IvanNaum/pwm_generator/imgs/E3.png

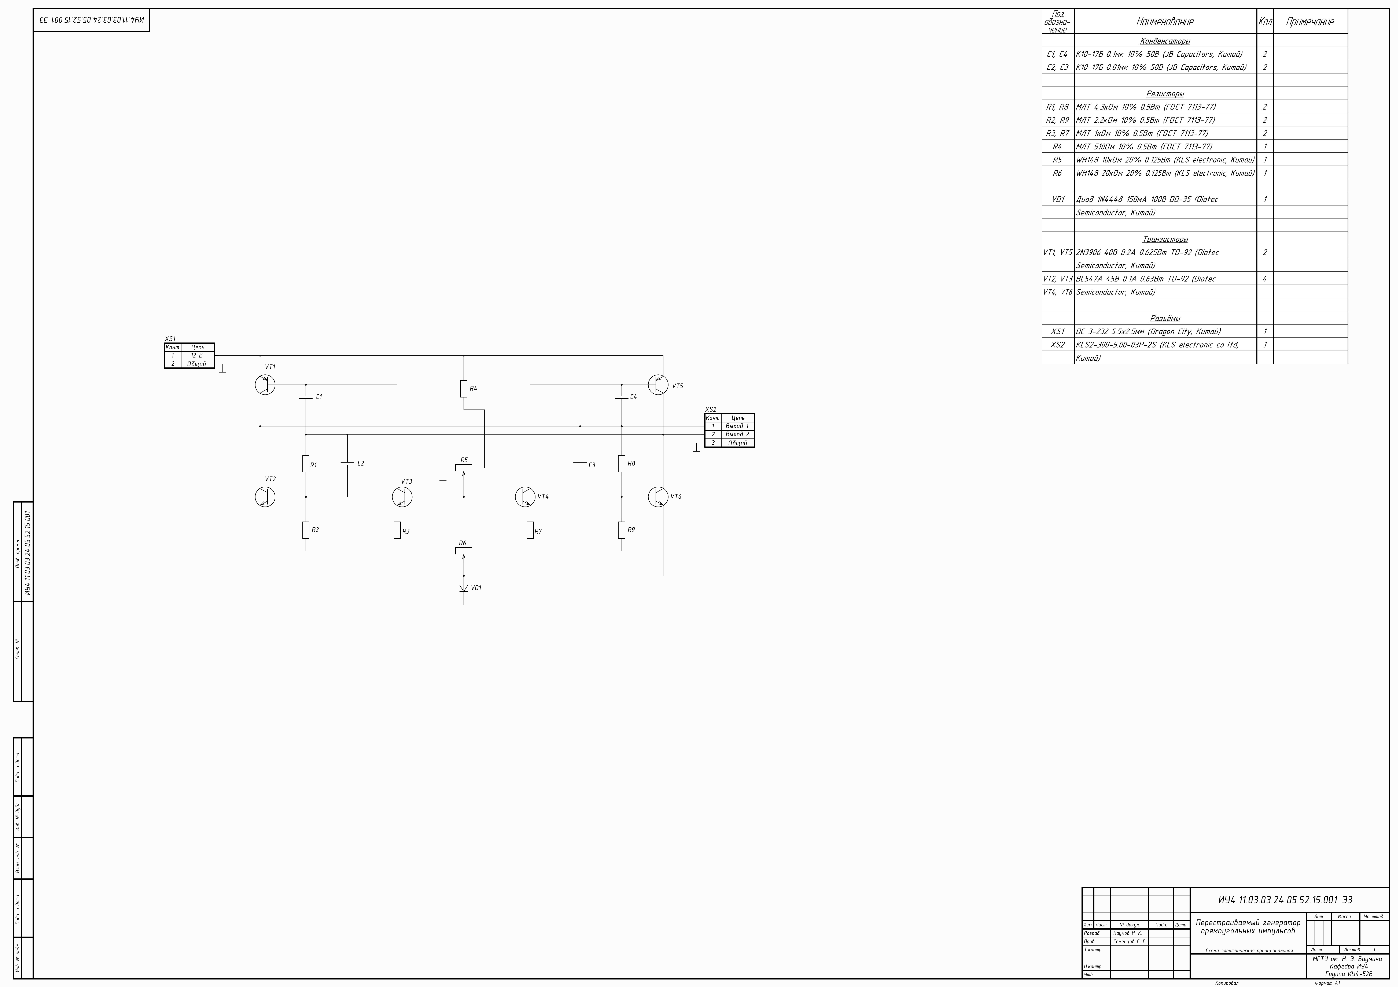
imgs/E3.png
