IvanNaum/pwm_generator/imgs/modeling.png

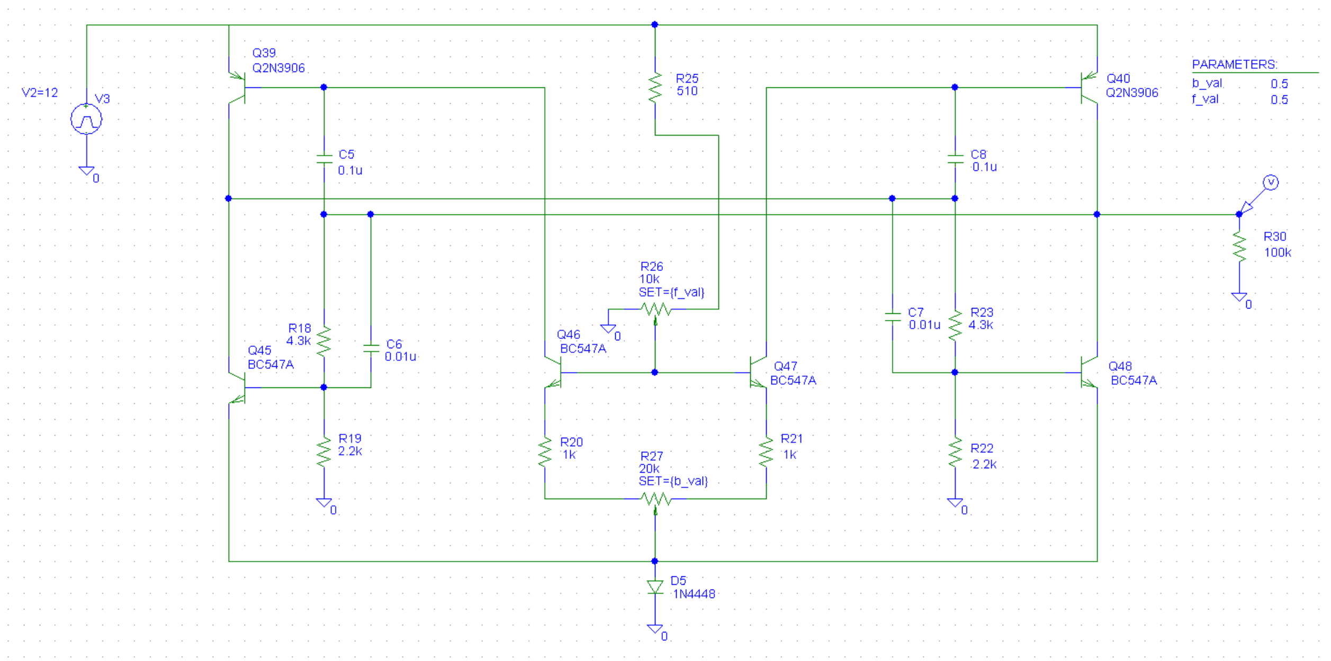
imgs/modeling.png
