IvanNaum/pwm_generator/imgs/modeling/1.png

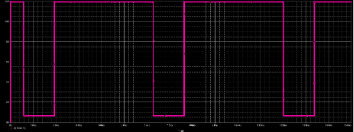
imgs/modeling/1.png
