IvanNaum/pwm_generator/imgs/modeling/2.png

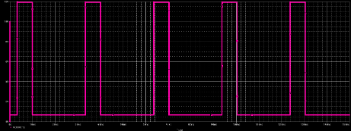
imgs/modeling/2.png
