IvanNaum/pwm_generator/imgs/modeling/3.png

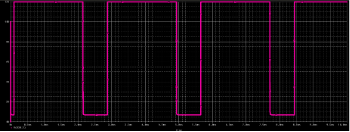
imgs/modeling/3.png
