IvanNaum/pwm_generator/imgs/modeling/4.png

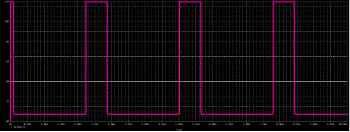
imgs/modeling/4.png
