IvanNaum/pwm_generator/imgs/modeling/inv_3.png

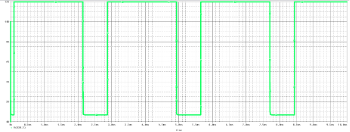
imgs/modeling/inv_3.png
