IvanNaum/pwm_generator/imgs/oscilloscope/002.BMP

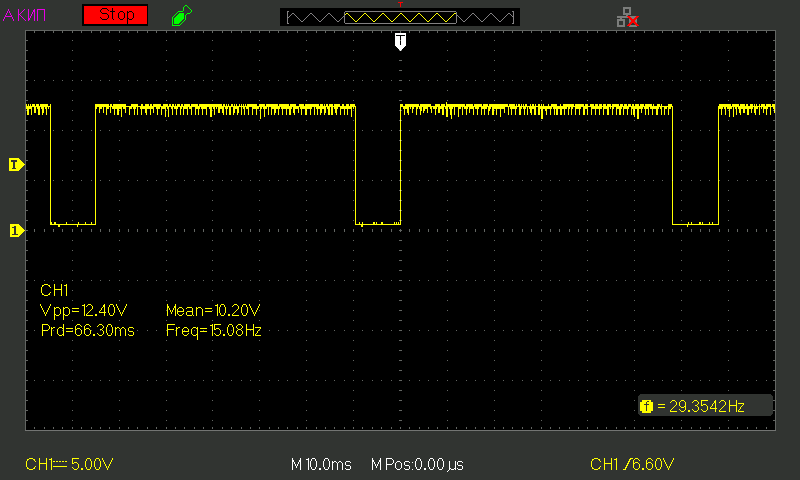
imgs/oscilloscope/002.BMP
