IvanNaum/pwm_generator/imgs/oscilloscope/003.BMP

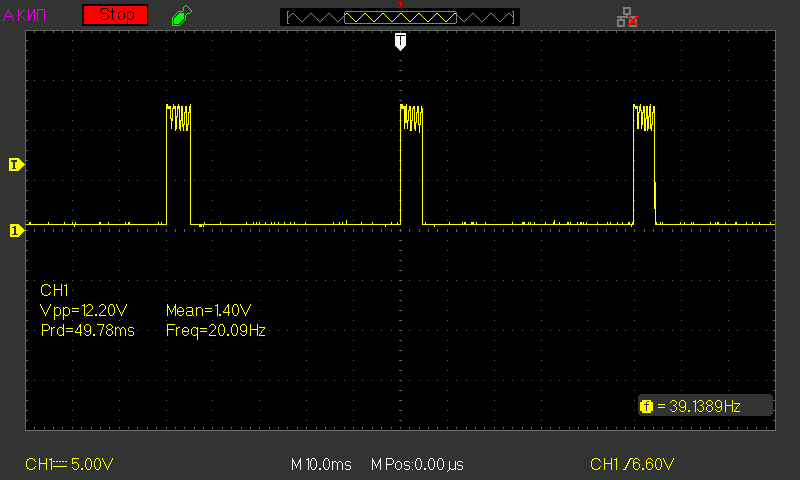
imgs/oscilloscope/003.BMP
