IvanNaum/pwm_generator/imgs/oscilloscope/004.BMP

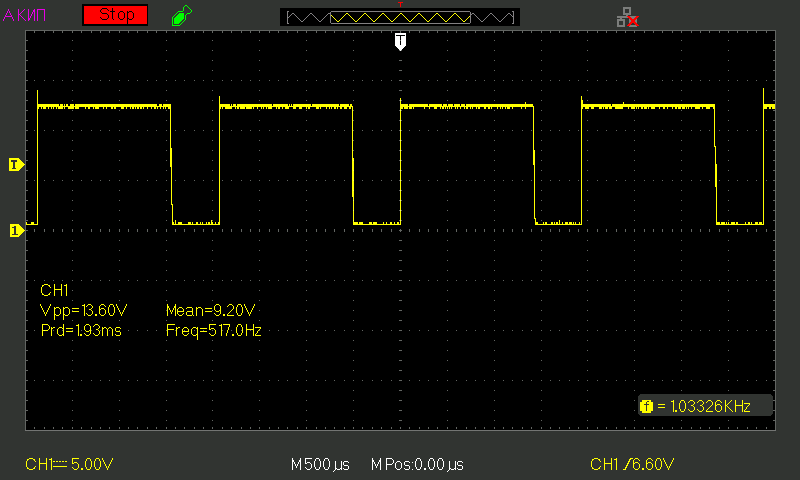
imgs/oscilloscope/004.BMP
