IvanNaum/pwm_generator/imgs/oscilloscope/005.BMP

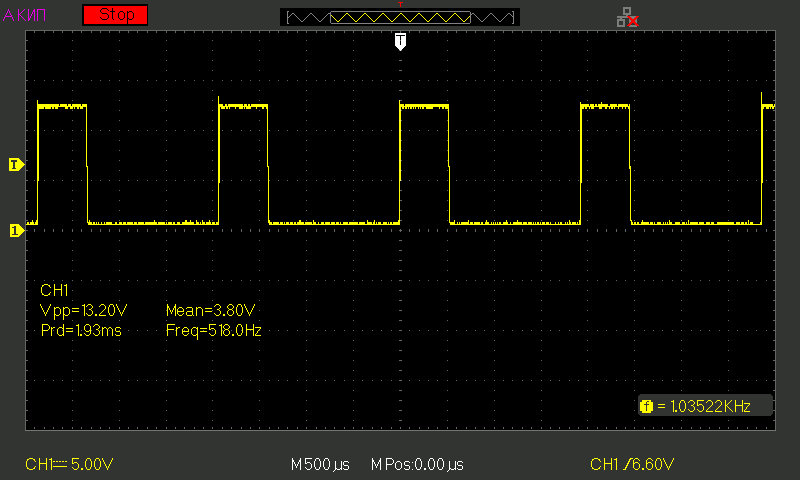
imgs/oscilloscope/005.BMP
