IvanNaum/pwm_generator/imgs/oscilloscope/inv_002.BMP

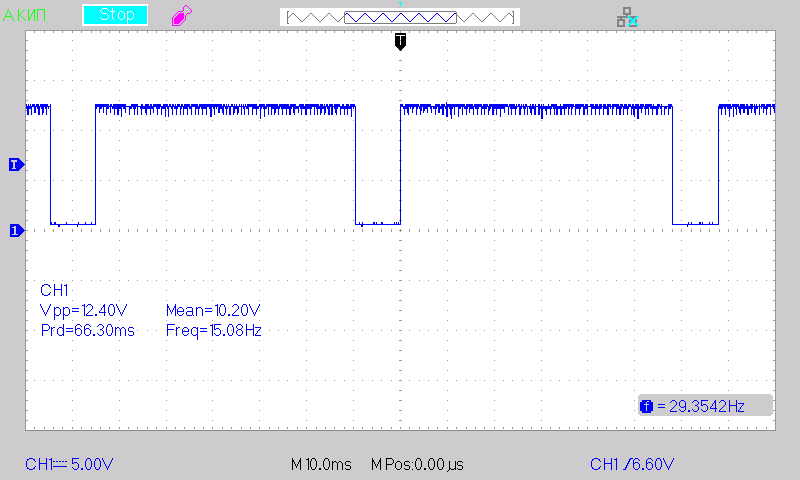
imgs/oscilloscope/inv_002.BMP
