IvanNaum/pwm_generator/imgs/oscilloscope/inv_004.BMP

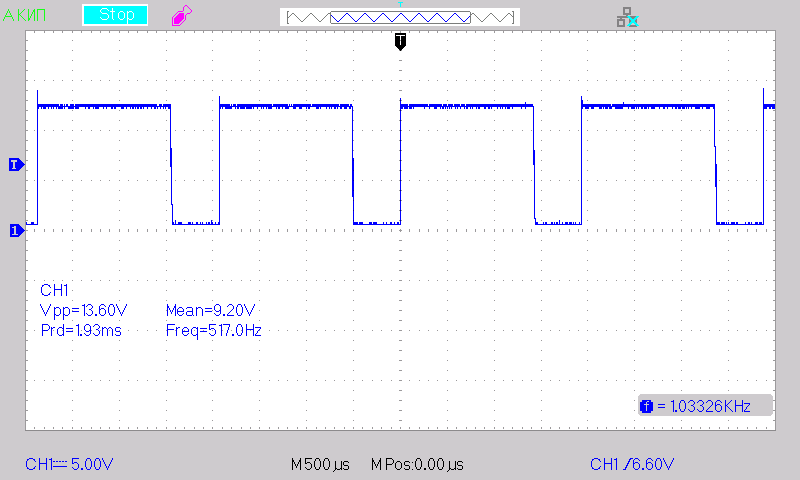
imgs/oscilloscope/inv_004.BMP
