IvanNaum/pwm_generator/imgs/oscilloscope/inv_005.BMP

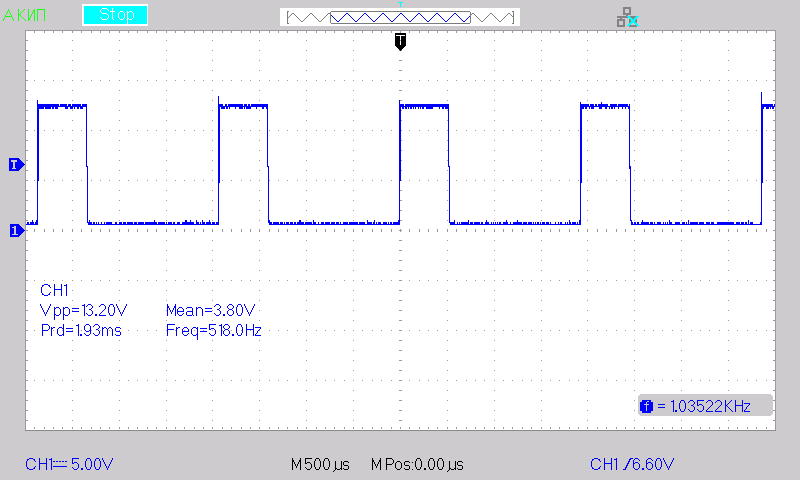
imgs/oscilloscope/inv_005.BMP
